bmoniey/teensy_baby8/doc/pics/IMG_2281.JPG

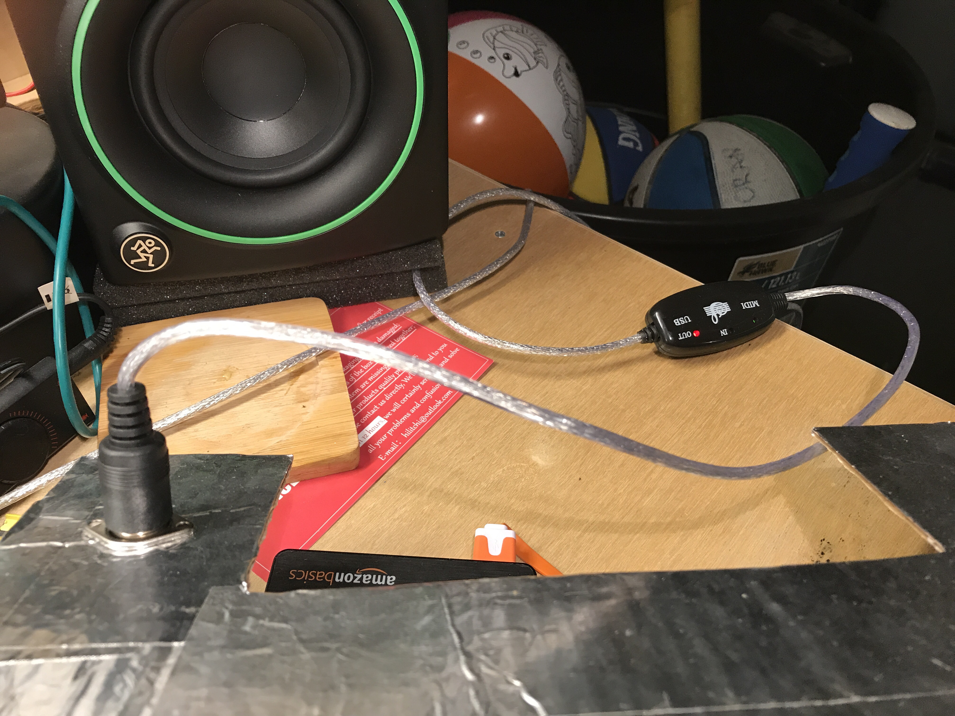
doc/pics/IMG_2281.JPG
