bmoniey/teensy_baby8/src/midi8/Midi.h

/**
*MIDI Percussion Key Map
*/
enum MidiPercGeneral{	
Acoustic_Bass_Drum = 35,
BassDrum1,
AcousticBassDrum,
BassDrum1,
SideStick,
AcousticSnare,
HandClap,
ElectricSnare,
LowFloorTom,
ClosedHiHat,
HighFloorTom,
PedalHiHat,
LowTom,
OpenHiHat,
LowMidTom,
HiMidTom,
CrashCymbal1,
HighTom,
RideCymbal1,
ChineseCymbal,
RideBell,
Tambourine,
SplashCymbal,
Cowbell,
CrashCymbal2,
Vibraslap,
RideCymbal2,
HiBongo,
LowBongo,
MuteHiConga,
OpenHiConga,
LowConga,
HighTimbale,
LowTimbale,
HighAgogo,
LowAgogo,
Cabasa,
Maracas,
ShortWhistle,
LongWhistle,
ShortGuiro,
LongGuiro,
Claves,
HiWoodBlock,
LowWoodBlock,
MuteCuica,
OpenCuica,
MuteTriangle,
OpenTriangle
};
