bmoniey/teensy_baby8/src/midi8/Notes.h

/**
*Notes.h
*/
#ifndef NOTES_H
#define NOTES_H
	#define OCTAVE_LIST_SIZE 11
	#define OCTAVE_LIST "C-2","C-1","C0","C1","C2","C3","C4","C5","C6","C7","C8"
	#define NOTES_LIST_SIZE 12
  #define OCTAVE_MIDDLE_C_IDX 5
	#define NOTE_LIST_SHARP "C","C#","D","D#","E","F","F#","G","G#","A","A#","B"
	#define NOTE_LIST_FLAT  "C","Db","D","Eb","E","F","Gb","G","Ab","A","Bb","B"
#endif
