bmoniey/teensy_baby8/doc/pics/IMG_2282.JPG

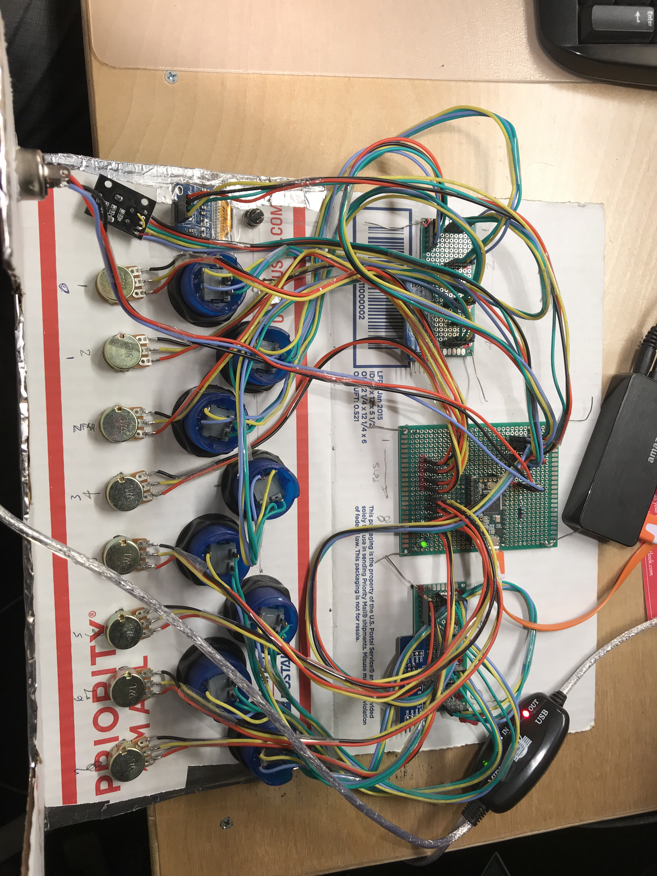
doc/pics/IMG_2282.JPG
